jpetkauskas/Hybrid-Buzzer/buzzer_transmitter/main/wireless.h

#pragma once

#include <stdint.h>
#include "esp_netif.h"
#include "esp_now.h"
#include "esp_wifi.h"
#include "nvs_flash.h"
#include <string.h>
#include "led.h"
#include "freertos/semphr.h"
#include "packet.h"

static const uint8_t DEFAULT_MAC_VALUE[6] = {0xFF,0xFF,0xFF,0xFF,0xFF,0xFF};

extern uint8_t receiver_mac[6];

extern esp_now_peer_info_t peer;

static SemaphoreHandle_t received_sem;

/* Updated by sync_recv_callback; read from IRAM button ISR — must be in RAM. */
extern volatile int64_t sync_base_us;
extern volatile uint8_t local_epoch;

void init_transmitter_wireless(void);

static void wireless_hardware_init(void);

void on_recv(const esp_now_recv_info_t *info, const uint8_t *data, int len);
